kongaskristjan/CameraMod/hardware/pcb/Camera.kicad_sch

## KiCad design hardware/pcb/Camera.kicad_sch (2022-01-30)

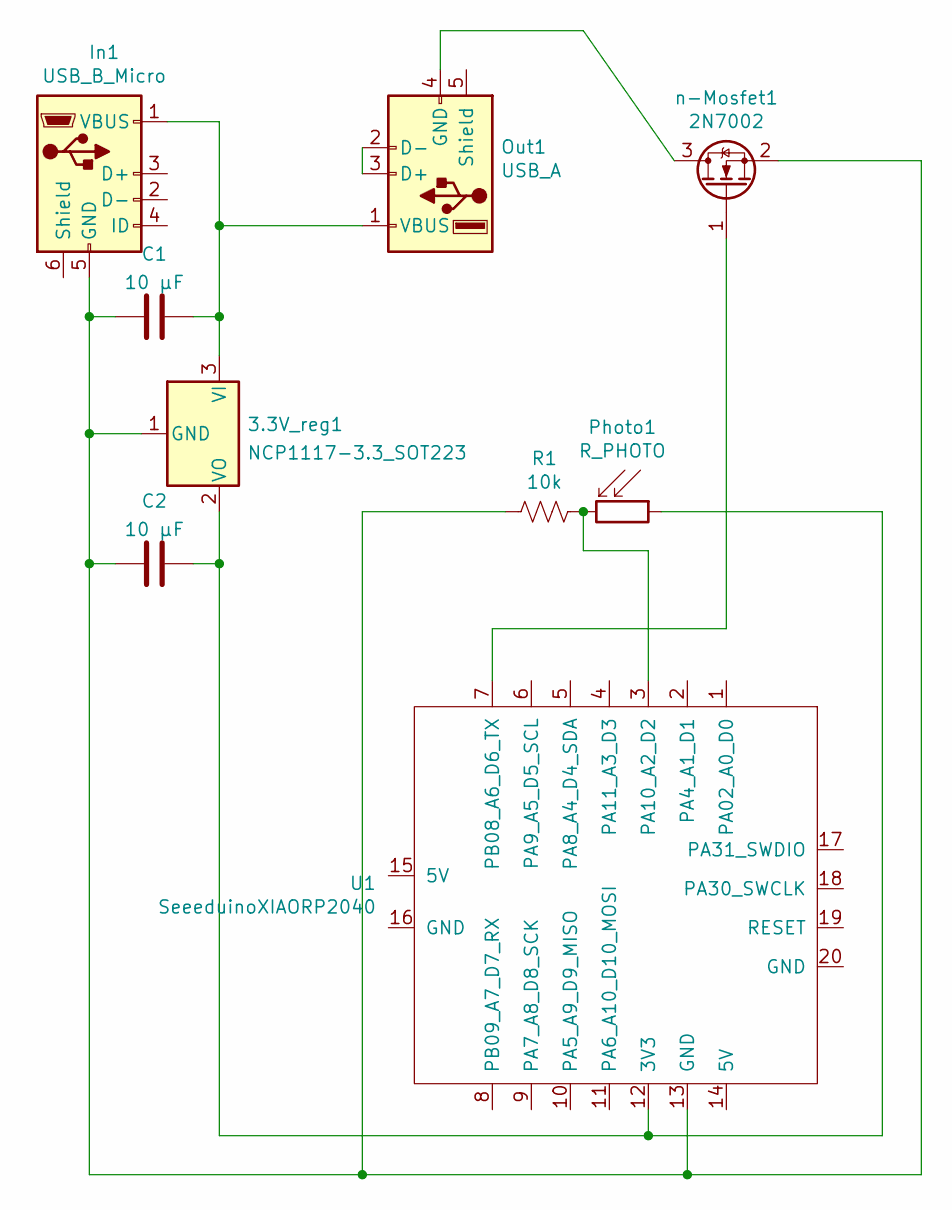
[picture p3: schematic Camera.kicad_sch]

Parts:
3.3V_reg1: NCP1117-3.3_SOT223; SOT-223-3_TabPin2
C1, C2: 10 μF; C_0805_2012Metric_Pad1.18x1.45mm_HandSolder
In1: USB_B_Micro; USB_Micro-B_Molex-105017-0001
Out1: USB_A; USB_A_Molex_67643_Horizontal
Photo1: R_PHOTO; R_Axial_DIN0411_L9.9mm_D3.6mm_P12.70mm_Horizontal
R1: 10k; R_0805_2012Metric_Pad1.20x1.40mm_HandSolder
U1: SeeeduinoXIAORP2040; Seeeduino XIAO
n-Mosfet1: 2N7002; SOT-23

Connections:
unnamed: 3.3V_reg1.1 (GND), C1.1, C2.1, In1.5 (GND), R1.2, U1.13 (GND), n-Mosfet1.2 (S)
unnamed: 3.3V_reg1.2 (VO), C2.2, Photo1.1, U1.12 (3V3)
unnamed: 3.3V_reg1.3 (VI), C1.2, In1.1 (VBUS), Out1.1 (VBUS)
unnamed: Out1.2 (D-), Out1.3 (D+)
unnamed: Out1.4 (GND), n-Mosfet1.3 (D)
unnamed: Photo1.2, R1.1, U1.3 (PA10_A2_D2)
unnamed: U1.7 (PB08_A6_D6_TX), n-Mosfet1.1 (G)
